Leito-uwu/PROYECTO-VaCaRu/05-Códigos/Esclavo/Brazo_Modularizado/Brazo_Modularizado.ino

#include <Wire.h>
#include <ESP32Servo.h>
#include "brazo.h"

void setup() {
  Serial.begin(9600);
  inicializarBrazo();
  Serial.println("Brazo en reposo. Esperando comandos...");
}

void loop() {
  if (!emergencia) {
    if (comandoNuevo) {
      procesarComando();
    }
  }
}
